mlilley/dxp480t-case/assets/004_rearcorner.jpg

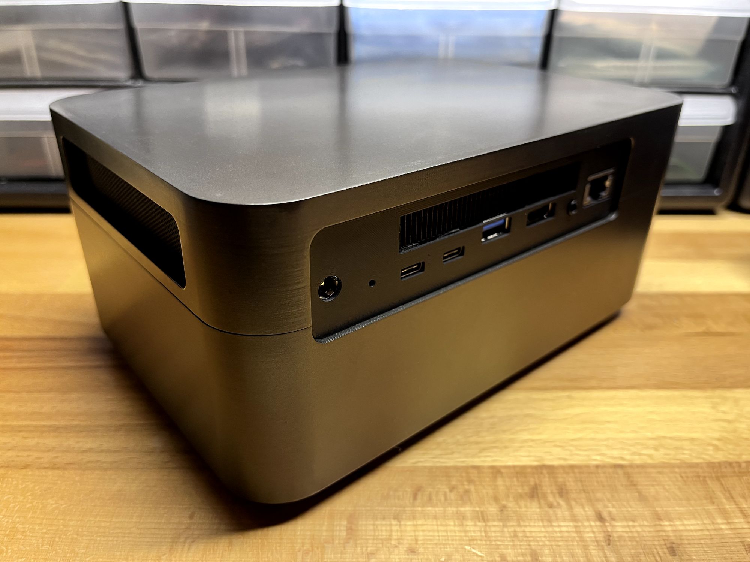
assets/004_rearcorner.jpg
