mlilley/dxp480t-case/assets/005_comparison.jpg

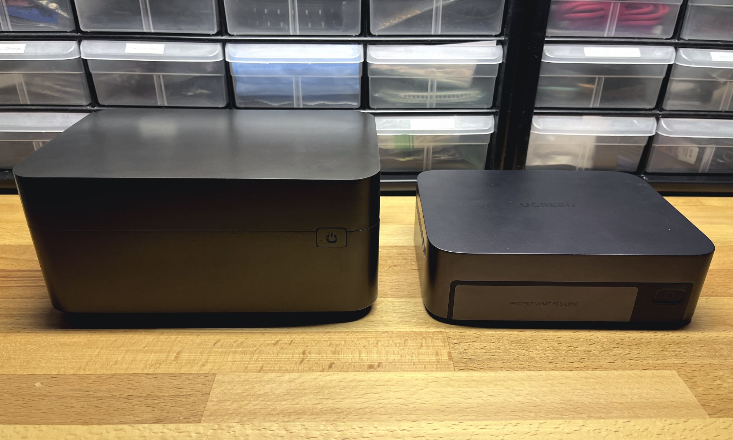
assets/005_comparison.jpg
