mlilley/dxp480t-case/assets/006_underside.png

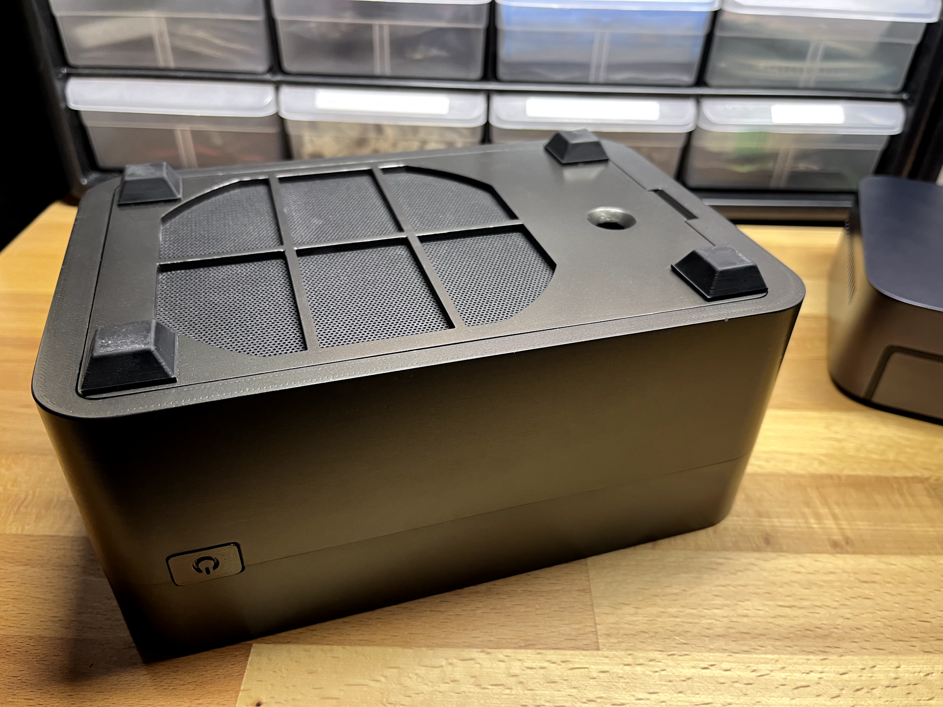
assets/006_underside.png
