mlilley/dxp480t-case/assets/009_cad1.png

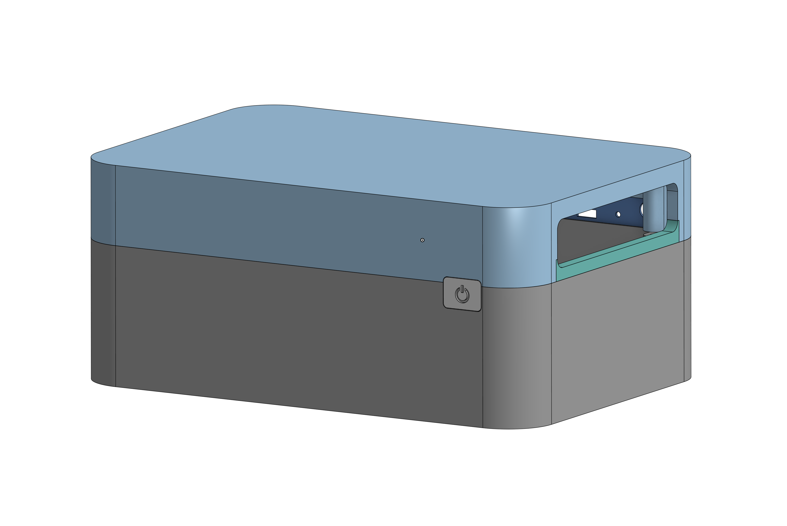
assets/009_cad1.png
