mlilley/dxp480t-case/cad/Case - bottom.step

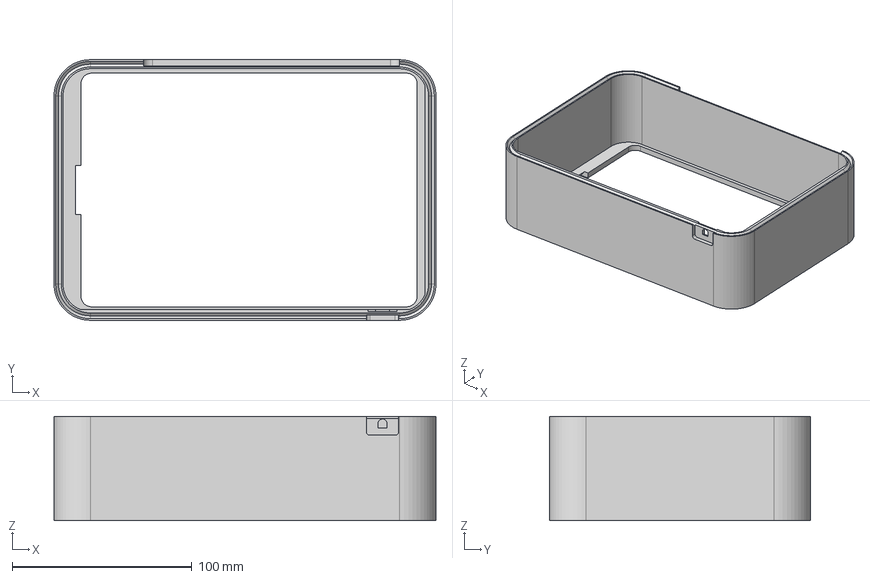
[picture p26: CAD file, 2024-08-06]
cad/Case - bottom.step
212.5 x 145.0 x 58.0 mm
