mlilley/dxp480t-case/cad/Case - standoff 2.step

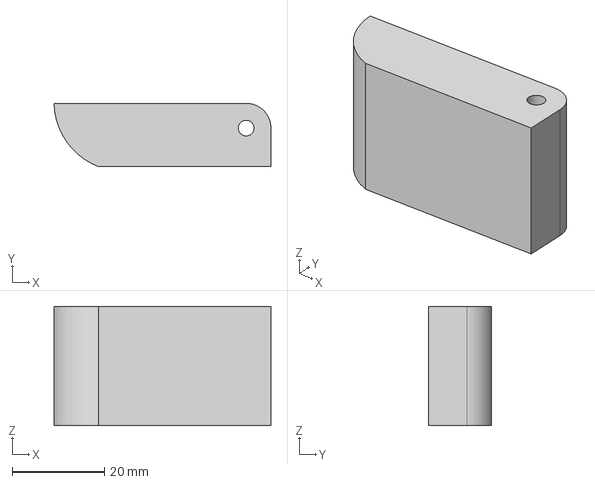
[picture p27: CAD file, 2024-08-06]
cad/Case - standoff 2.step
47.0 x 13.7 x 25.8 mm
